indoor-industry/Mercurio-RevB/Module/Case_9mm/tft-lcd-2-8-inch-ili9341-touch-320x240-1.snapshot.22/TFT LCD 2.8 inch ILI9341 2.png

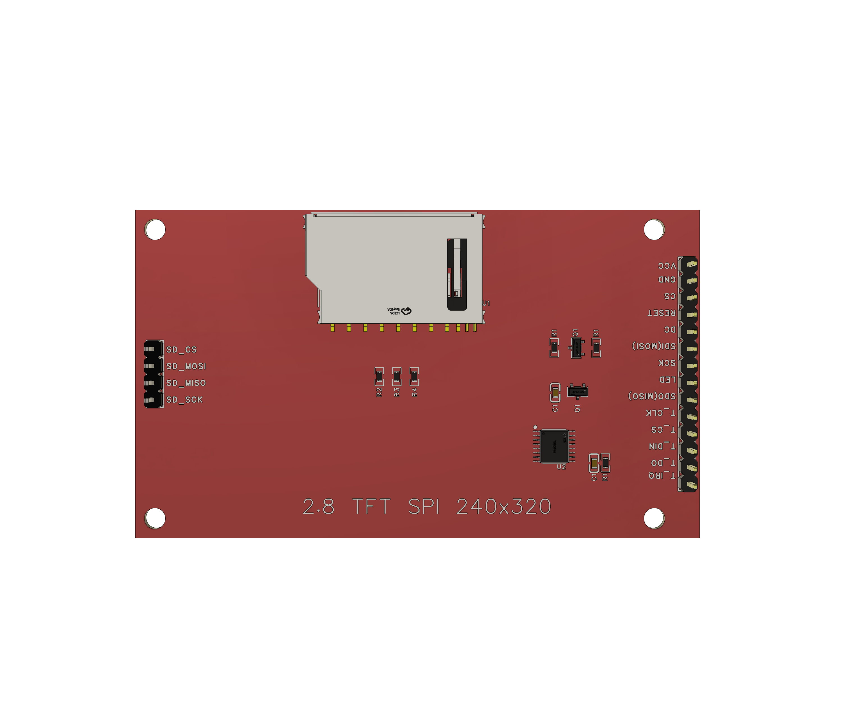
Module/Case_9mm/tft-lcd-2-8-inch-ili9341-touch-320x240-1.snapshot.22/TFT LCD 2.8 inch ILI9341 2.png
